inmbolmie/T4_EGA_VGA/ega2vga/VGA_t4.h

/*
	This file is part of VGA_t4 library.

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
	Copyright (C) 2020 J-M Harvengt

	Inspired from the original Teensy3 uVGA library of Eric PREVOTEAU.
	QTIMER/FlexIO code based on Teensy4 examples of KurtE, Manitou and easone 
	from the Teensy4 forum (https://forum.pjrc.com)
*/

#ifndef _VGA_T4_H
#define _VGA_T4_H

#include <Arduino.h>
#include <avr_emulation.h>
#include <DMAChannel.h>
#include <math.h>


// Enable debug info (requires serial initialization)
#define DEBUG

// Enable 12bits mode
// Default is 8bits RRRGGGBB (332) 
// But 12bits GBB0RRRRGGGBB (444) feasible BUT NOT TESTED !!!!
//#define BITS12



#ifdef BITS12
typedef uint16_t vga_pixel;
#define VGA_RGB(r,g,b)  ( (((r>>3)&0x1f)<<11) | (((g>>2)&0x3f)<<5) | (((b>>3)&0x1f)<<0) )
#else
typedef uint8_t vga_pixel;
#define VGA_RGB(r,g,b)   ( (((r>>5)&0x07)<<5) | (((g>>5)&0x07)<<2) | (((b>>6)&0x3)<<0) )
#endif

typedef enum vga_mode_t
{
  VGA_MODE_320x240 = 0,
  VGA_MODE_320x480 = 1,
  VGA_MODE_352x240 = 2,
  VGA_MODE_352x480 = 3,
  VGA_MODE_512x240 = 4,
  VGA_MODE_512x480 = 5,
  VGA_MODE_640x240 = 6,
  VGA_MODE_640x480 = 7
} vga_mode_t;


typedef enum vga_error_t
{
	VGA_OK = 0,
	VGA_ERROR = -1
} vga_error_t;

#define MaxPolyPoint    100

#define AUDIO_SAMPLE_BUFFER_SIZE 256

// 2D point structure
typedef struct {
	int16_t x;			// X Coordinate on screen
	int16_t y;			// Y Coordinate on screen
}Point2D;

// Polygon structure
typedef struct {
	Point2D		Center;				// Polygon Center (point where the polygon can rotate arround)
	Point2D		Pts[MaxPolyPoint];	// Points for the polygon
}PolyDef;


#define DEFAULT_VSYNC_PIN 8

#ifndef ABS
#define ABS(X)  ((X) > 0 ? (X) : -(X))
#endif

extern PolyDef PolySet;  // polygon data to declare in c file


// Precomputed sinus and cosinus table from 0 to 359 degrees
// The tables are in Degrees not in Radian !
const float calcsi[360]={
		0.000001 ,                                                                                                                            //  0
		0.01745239 , 0.03489947 , 0.05233591 , 0.06975641 , 0.08715567 , 0.1045284 , 0.1218692 , 0.139173 , 0.1564343 , 0.173648 ,            // 1 à  10
		0.1908088 , 0.2079115 , 0.2249509 , 0.2419217 , 0.2588188 , 0.2756371 , 0.2923715 , 0.3090167 , 0.3255679 , 0.3420198 ,               // 11 à  20
		0.3583677 , 0.3746063 , 0.3907308 , 0.4067363 , 0.4226179 , 0.4383708 , 0.4539901 , 0.4694712 , 0.4848093 , 0.4999996 ,               // 21 à  30
		0.5150377 , 0.5299189 , 0.5446386 , 0.5591925 , 0.573576 , 0.5877848 , 0.6018146 , 0.615661 , 0.62932 , 0.6427872 ,                   // 31 à  40
		0.6560586 , 0.6691301 , 0.6819978 , 0.6946579 , 0.7071063 , 0.7193394 , 0.7313532 , 0.7431444 , 0.7547091 , 0.7660439 ,               // 41 à  50
		0.7771455 , 0.7880103 , 0.798635 , 0.8090165 , 0.8191515 , 0.8290371 , 0.8386701 , 0.8480476 , 0.8571668 , 0.8660249 ,                // 51 à  60
		0.8746193 , 0.8829472 , 0.8910061 , 0.8987936 , 0.9063074 , 0.913545 , 0.9205045 , 0.9271835 , 0.9335801 , 0.9396922 ,                // 61 à  70
		0.9455183 , 0.9510562 , 0.9563044 , 0.9612614 , 0.9659255 , 0.9702954 , 0.9743698 , 0.9781474 , 0.981627 , 0.9848075 ,                // 71 à  80
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
  vga_error_t begin(vga_mode_t mode, boolean* isr_fired, unsigned long  long 	cpu_freq);
  void begin_audio(int samplesize, void (*callback)(short * stream, int len));
  void end();
  void end_audio();
  void debug();
  void tweak_video(int shiftdelta, int numdelta, int denomdelta);

  // retrieve real size of the frame buffer
  void get_frame_buffer_size(int *width, int *height);

  // wait next Vsync
  void waitSync();
  void waitLine(int line);

  // =========================================================
  // graphic primitives
  // =========================================================

  void clear(vga_pixel col) ; 
  void drawPixel(int x, int y, vga_pixel color);
  vga_pixel getPixel(int x, int y);
  vga_pixel * getLineBuffer(int j);
  void start_isr_time_recording();
  void stop_isr_time_recording();
  boolean has_fired_isr() ;
  static boolean isr_fired;
  int get_fb_stride();
  vga_pixel * get_frame_buffer();
  unsigned long get_cycles_last_isr_start();
  unsigned long get_cycles_last_isr_end();
  int getFiredIsr();
  void drawRect(int16_t x, int16_t y, int16_t w, int16_t h, vga_pixel color);
  void drawText(int16_t x, int16_t y, const char * text, vga_pixel fgcolor, vga_pixel bgcolor, bool doublesize);
  void drawSprite(int16_t x, int16_t y, const int16_t *bitmap);
  void drawSprite(int16_t x, int16_t y, const int16_t *bitmap, uint16_t croparx, uint16_t cropary, uint16_t croparw, uint16_t croparh);
  void writeScreen(const vga_pixel *pcolors);  
  void writeLine(int width, int height, int y, vga_pixel *buf);
  void writeLine(int width, int height, int stride, uint8_t *buffer, vga_pixel *palette);
  void writeLine16(int width, int height, int y, uint16_t *buf);  
  void writeScreen(int width, int height, int stride, uint8_t *buffer, vga_pixel *palette);
  void copyLine(int width, int height, int ysrc, int ydst);

  // ************************************** GFX API extension from darthvader ******************************************************
  void drawline(int16_t x1, int16_t y1, int16_t x2, int16_t y2, vga_pixel color);
  void draw_h_line(int16_t x1, int16_t y1, int16_t lenght, vga_pixel color);
  void draw_v_line(int16_t x1, int16_t y1, int16_t lenght, vga_pixel color);
  void drawcircle(int16_t x, int16_t y, int16_t radius, vga_pixel color);
  void drawfilledcircle(int16_t x, int16_t y, int16_t radius, vga_pixel fillcolor, vga_pixel bordercolor);
  void drawellipse(int16_t cx, int16_t cy, int16_t radius1, int16_t radius2, vga_pixel color);
  void drawfilledellipse(int16_t cx, int16_t cy, int16_t radius1, int16_t radius2, vga_pixel fillcolor, vga_pixel bordercolor);
  void drawtriangle(int16_t ax, int16_t ay, int16_t bx, int16_t by, int16_t cx, int16_t cy, vga_pixel color);
  void drawfilledtriangle(int16_t ax, int16_t ay, int16_t bx, int16_t by, int16_t cx, int16_t cy, vga_pixel fillcolor, vga_pixel bordercolor);
  void drawquad(int16_t centerx, int16_t centery, int16_t w, int16_t h, int16_t angle, vga_pixel color);
  void drawfilledquad(int16_t centerx, int16_t centery, int16_t w, int16_t h, int16_t angle, vga_pixel fillcolor, vga_pixel bordercolor);
  void drawpolygon(int16_t cx, int16_t cy, vga_pixel bordercolor);
  void drawfullpolygon(int16_t cx, int16_t cy, vga_pixel fillcolor, vga_pixel bordercolor);
  void drawrotatepolygon(int16_t cx, int16_t cy, int16_t Angle, vga_pixel fillcolor, vga_pixel bordercolor, uint8_t filled);
  // *******************************************************************************************************************************

  

  // =========================================================
  // Game engine
  // =========================================================

  #define TILES_MAX_LAYERS  2

  // 16x16 pixels tiles or 8x8 if USE_8PIXTILES is set
  //#define USE_8PIXTILES 1
  #ifdef USE_8PIXTILES
  #define TILES_COLS        40
  #define TILES_ROWS        30
  #define TILES_W           8
  #define TILES_H           8
  #define TILES_HBITS       3
  #define TILES_HMASK       0x7
  #else
  #define TILES_COLS        20
  #define TILES_ROWS        15
  #define TILES_W           16
  #define TILES_H           16
  #define TILES_HBITS       4
  #define TILES_HMASK       0xf
  #endif
  
  // 32 sprites 16x32 or max 64 16x16 (not larger!!!)
  #define SPRITES_MAX       32
  #define SPRITES_W         16
  #define SPRITES_H         32

  void begin_gfxengine(int nblayers, int nbtiles, int nbsprites);
  void run_gfxengine();
  void tile_data(unsigned char index, vga_pixel * data, int len);
  void sprite_data(unsigned char index, vga_pixel * data, int len);
  void sprite(int id , int x, int y, unsigned char index);
  void sprite_hide(int id);
  void tile_draw(int layer, int x, int y, unsigned char index);
  void tile_draw_row(int layer, int x, int y, unsigned char * data, int len);
  void tile_draw_col(int layer, int x, int y, unsigned char * data, int len);
  void set_hscroll(int layer, int rowbeg, int rowend, int mask);
  void set_vscroll(int layer, int colbeg, int colend, int mask);
  void hscroll(int layer, int value);
  void vscroll(int layer, int value);


private:
  static uint8_t _vsync_pin;
  static DMAChannel flexio1DMA;
  static DMAChannel flexio2DMA; 
  static void QT3_isr(void);
  static void AUDIO_isr(void);  
  static void SOFTWARE_isr(void);  
};


#endif
